hcknbrgr/Cartpole/FinalTraining/EpisodeDuration2381.pdf

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

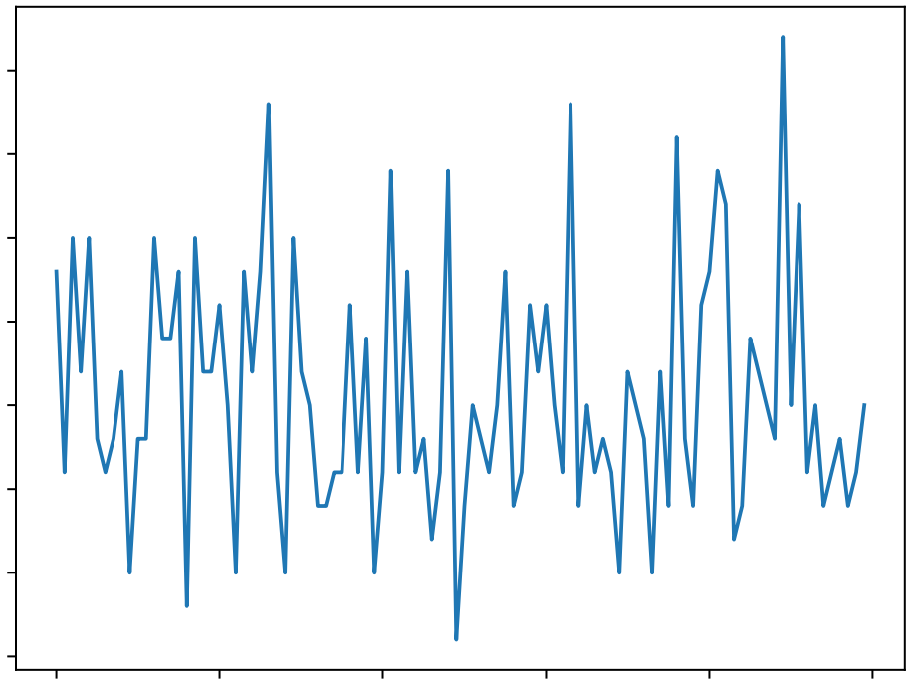
[picture p1: figure]
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
