hcknbrgr/Cartpole/FinalTraining/EpisodeDuration1756.pdf

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

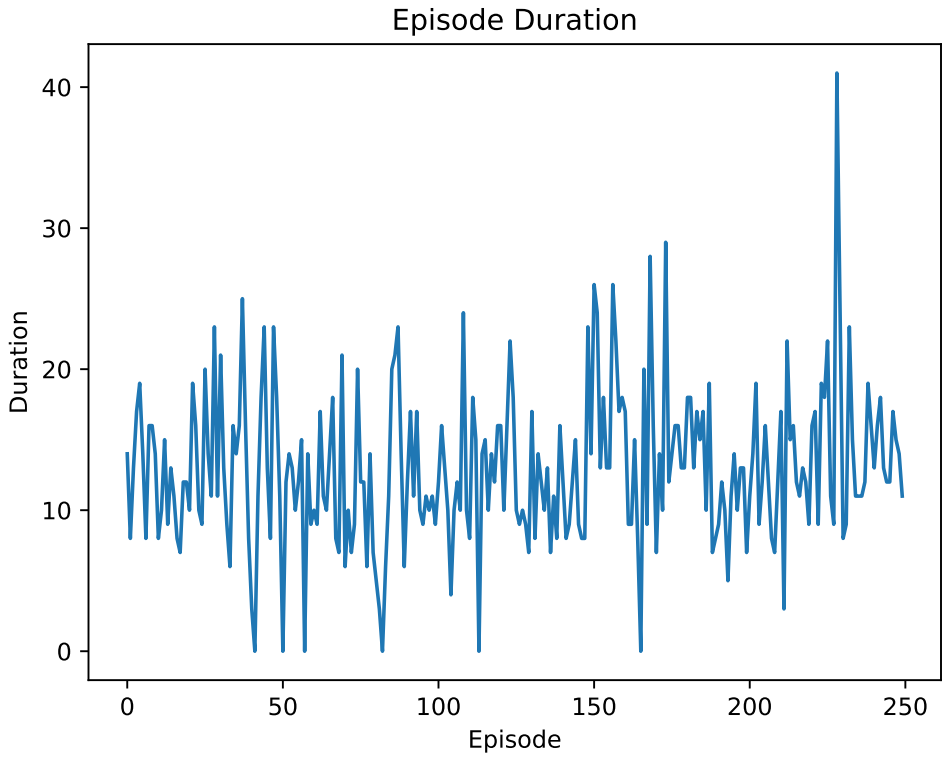
[picture p25: page 1]
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
