hcknbrgr/Cartpole/FinalTraining/EpisodeDuration2007.pdf

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

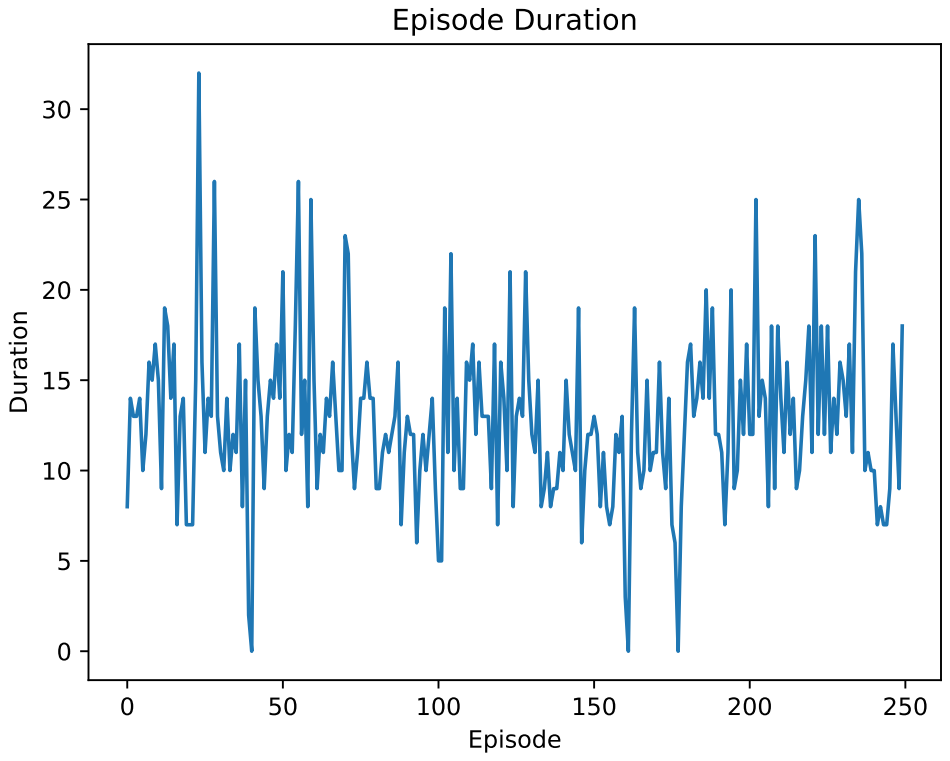
[picture p26: page 1]
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
