hcknbrgr/Cartpole/FinalTraining/EpisodeDuration752.pdf

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

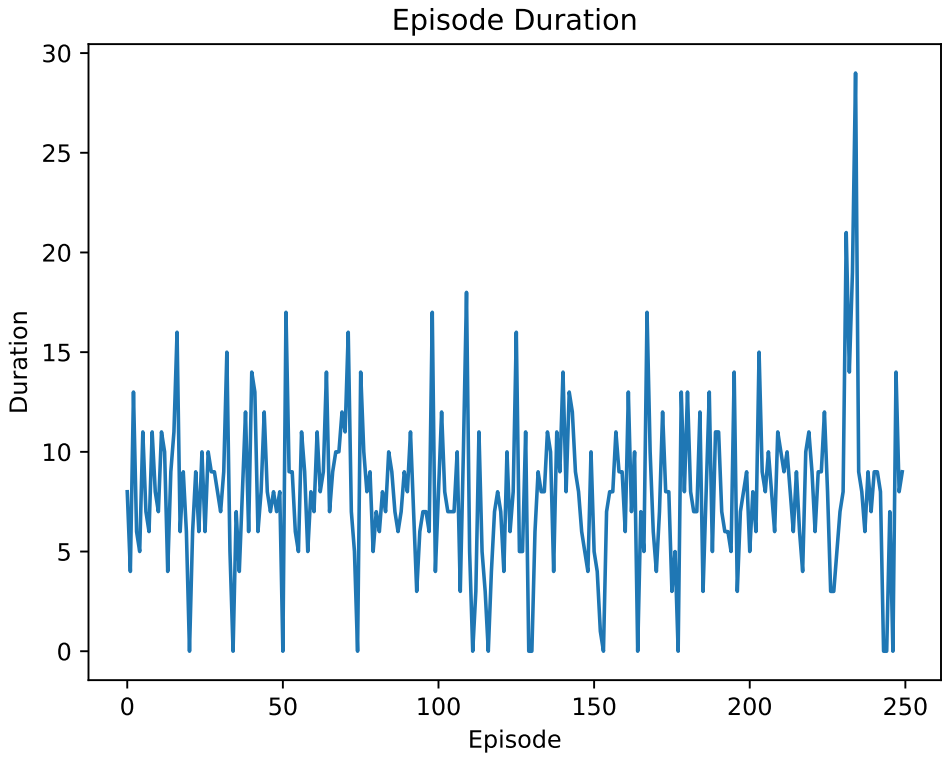
[picture p30: page 1]
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
